SeanP2001/Pico_Handheld_Games_Console/Images/Breadboard_Prototype.jpg

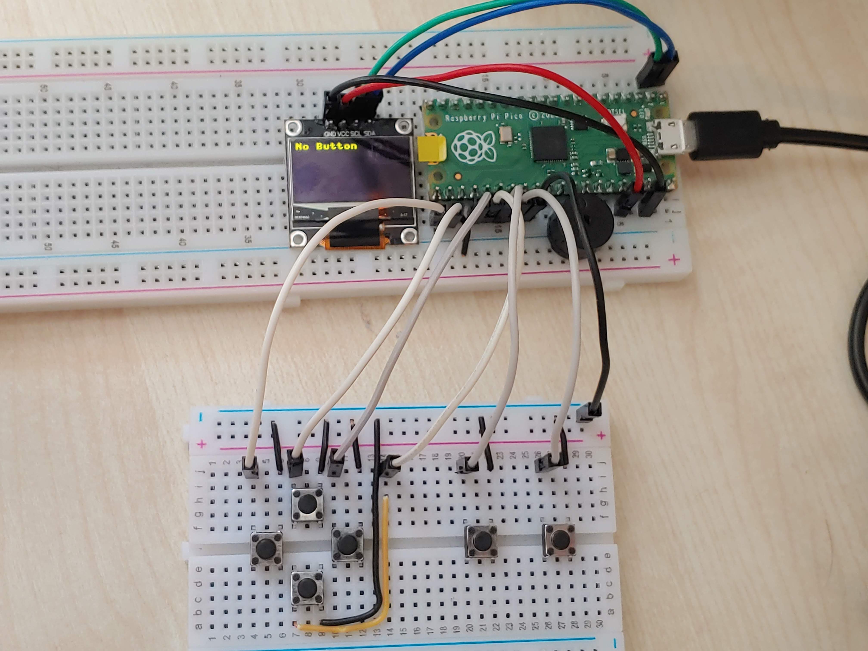
Images/Breadboard_Prototype.jpg
