SeanP2001/Pico_Handheld_Games_Console/Images/Display_Jumpers.jpg

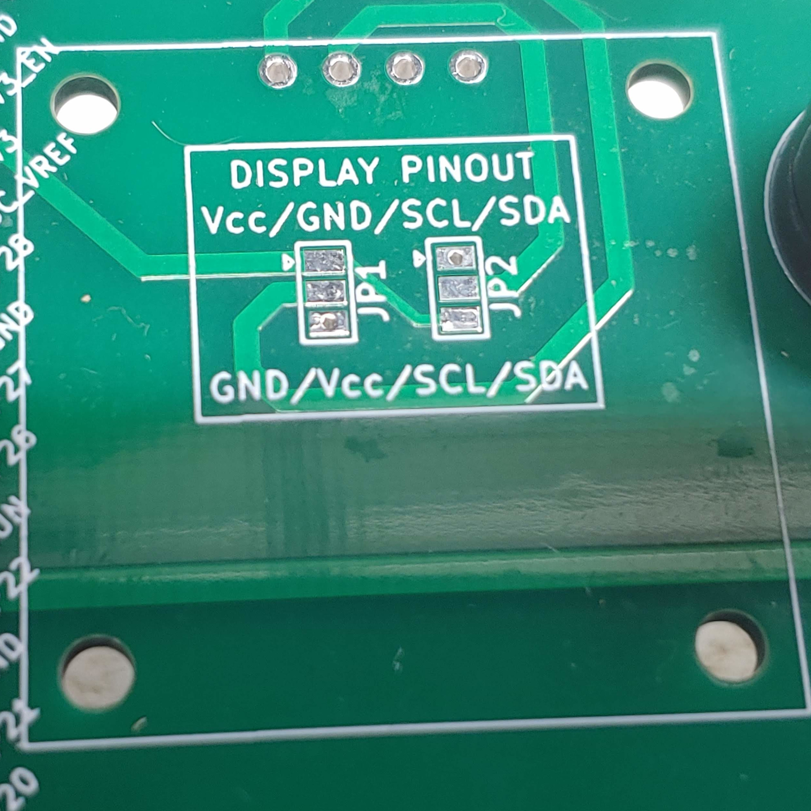
Images/Display_Jumpers.jpg
