SeanP2001/Pico_Handheld_Games_Console/Images/Display_Jumpers_Kapton_Tape.jpg

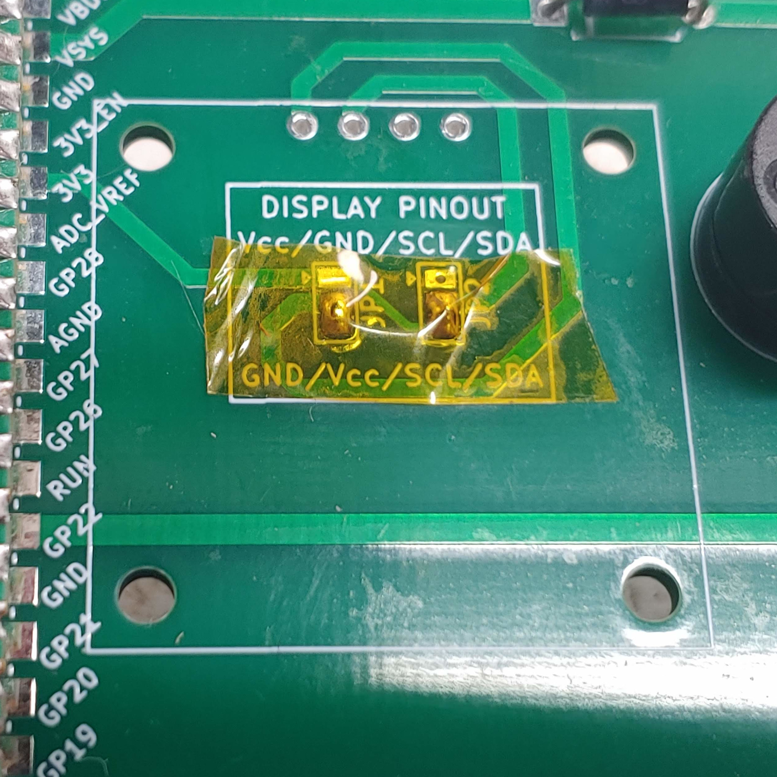
Images/Display_Jumpers_Kapton_Tape.jpg
