SeanP2001/Pico_Handheld_Games_Console/PCB/Pico_Handheld/SVG_Out/PNG/Pico_Handheld-B_Fab.png

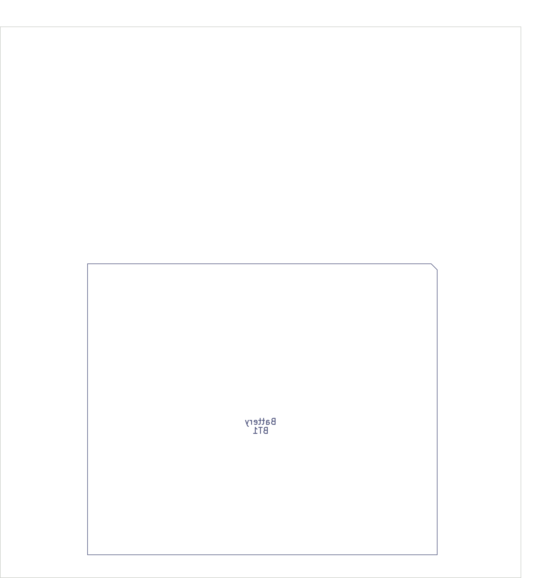
PCB/Pico_Handheld/SVG_Out/PNG/Pico_Handheld-B_Fab.png
