SeanP2001/Pico_Handheld_Games_Console/PCB/Pico_Handheld/SVG_Out/PNG/Pico_Handheld-Edge_Cuts.png

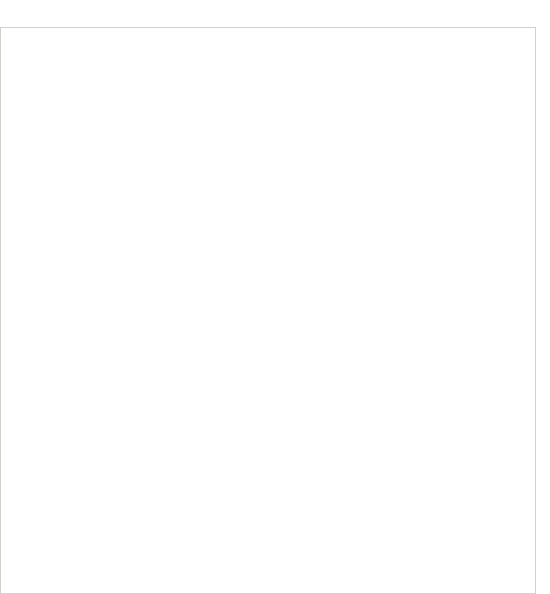
PCB/Pico_Handheld/SVG_Out/PNG/Pico_Handheld-Edge_Cuts.png
