SeanP2001/Pico_Handheld_Games_Console/PCB/Pico_Handheld/SVG_Out/PNG/Pico_Handheld-F_Cu.png

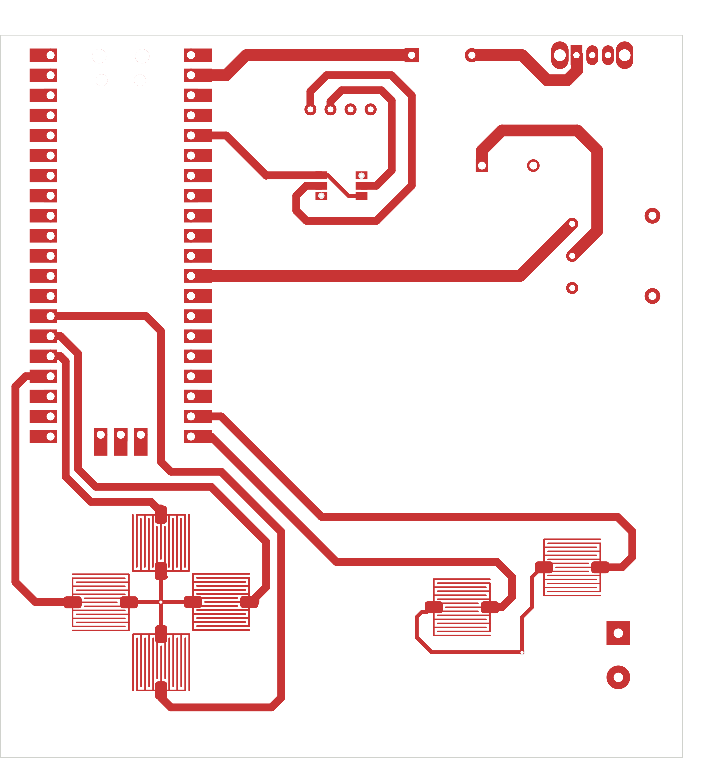
PCB/Pico_Handheld/SVG_Out/PNG/Pico_Handheld-F_Cu.png
